verdanatesman/STM32-ile-BLDC-Motor-Surucu-Karti-Tasarimi-ve-Uretimi/Tasarım görseller/ek3.jpeg

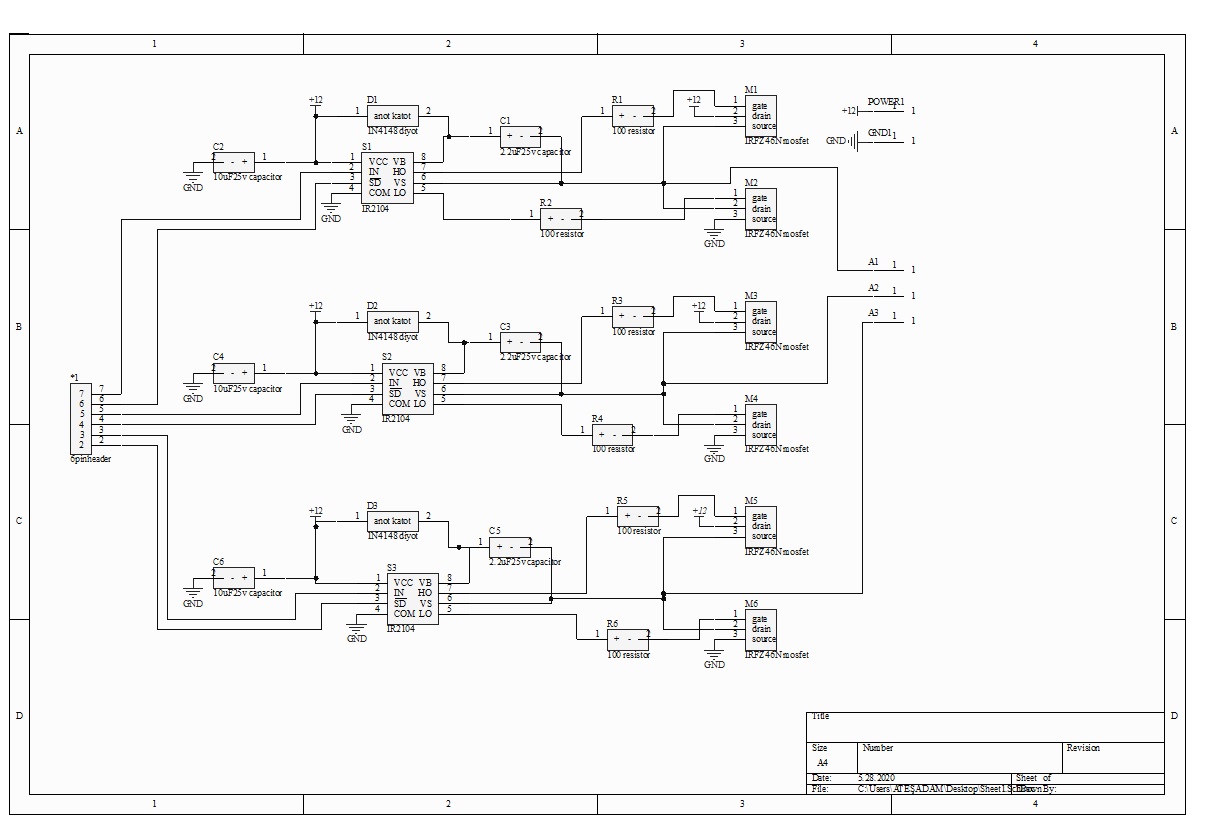
Tasarım görseller/ek3.jpeg
