verdanatesman/STM32-ile-BLDC-Motor-Surucu-Karti-Tasarimi-ve-Uretimi/Tasarım görseller/ek4.jpeg

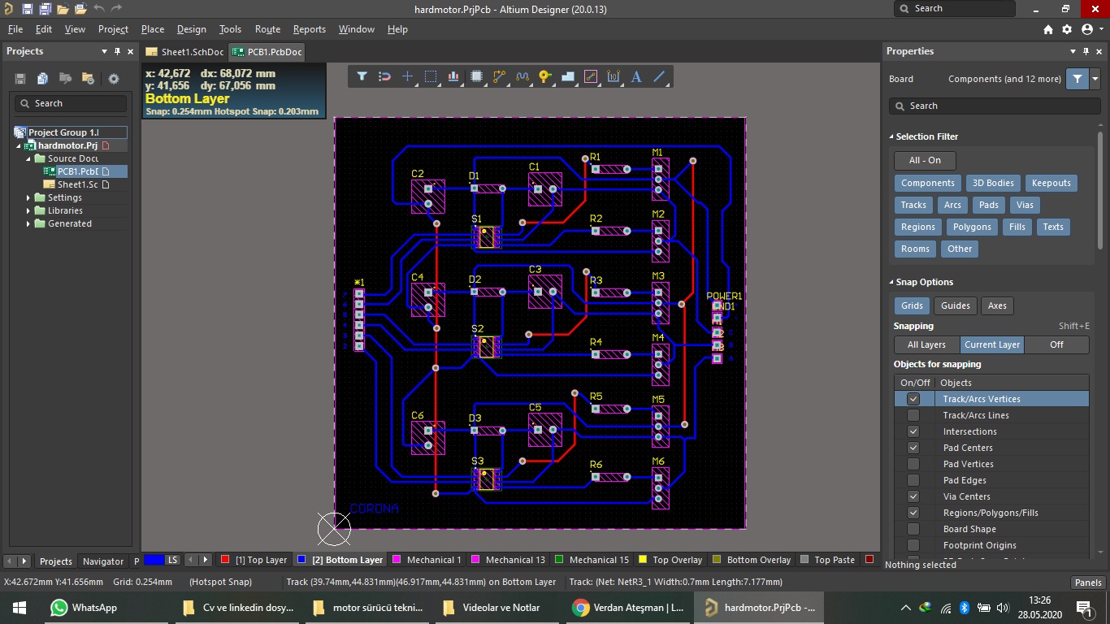
Tasarım görseller/ek4.jpeg
