verdanatesman/STM32-ile-BLDC-Motor-Surucu-Karti-Tasarimi-ve-Uretimi/Uretim gorselleri/ek7.jpeg

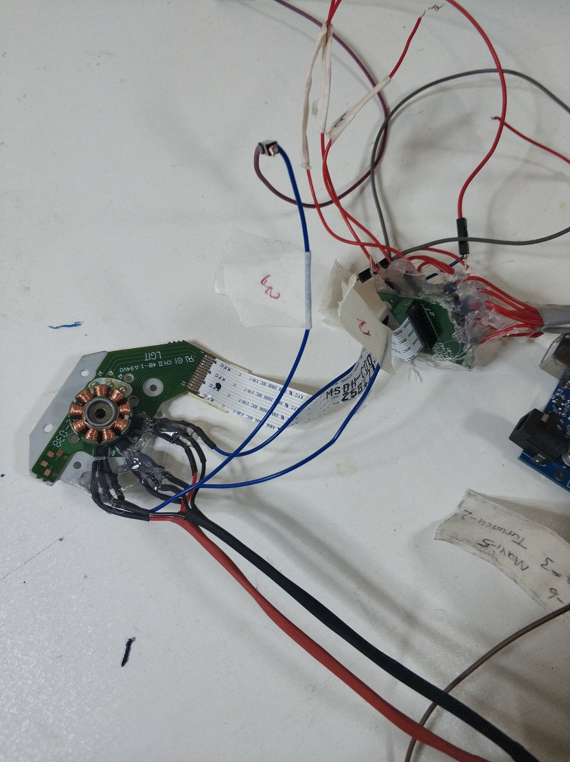
Uretim gorselleri/ek7.jpeg
