verdanatesman/STM32-ile-BLDC-Motor-Surucu-Karti-Tasarimi-ve-Uretimi/Uretim gorselleri/ek8.jpeg

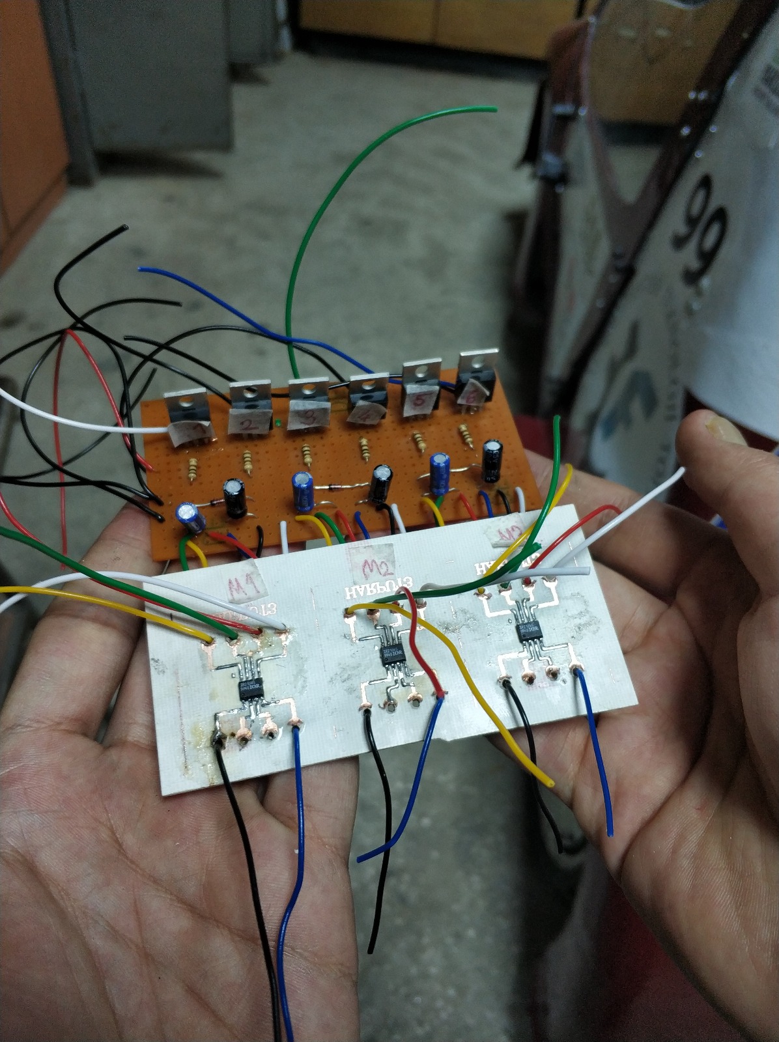
Uretim gorselleri/ek8.jpeg
