verdanatesman/STM32-ile-BLDC-Motor-Surucu-Karti-Tasarimi-ve-Uretimi/Uretim gorselleri/ek11.jpeg

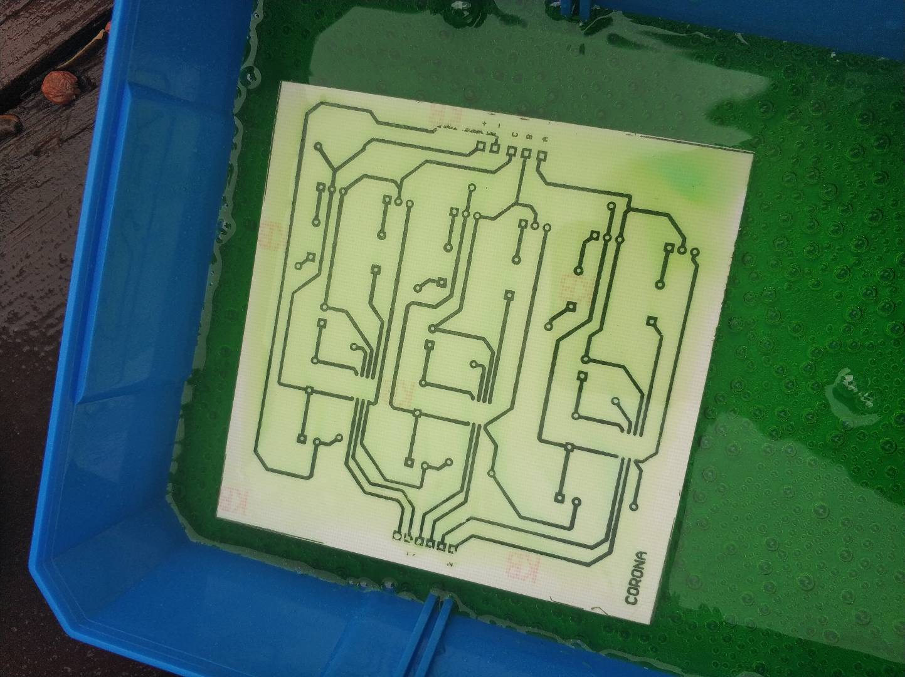
Uretim gorselleri/ek11.jpeg
