verdanatesman/STM32-ile-BLDC-Motor-Surucu-Karti-Tasarimi-ve-Uretimi/Uretim gorselleri/ek12.jpeg

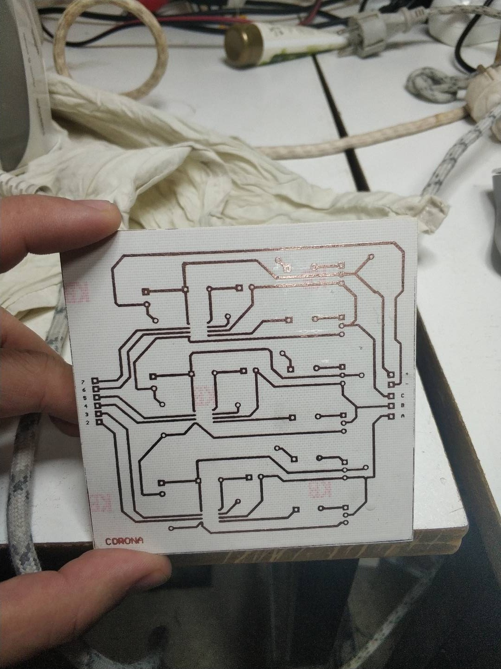
Uretim gorselleri/ek12.jpeg
