verdanatesman/STM32-ile-BLDC-Motor-Surucu-Karti-Tasarimi-ve-Uretimi/Uretim gorselleri/ek13.jpeg

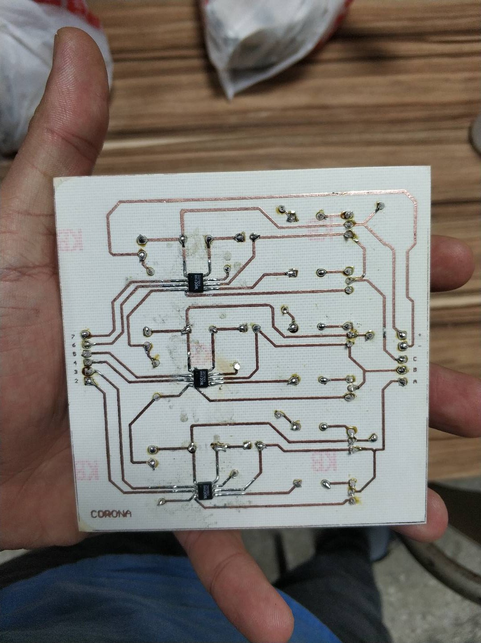
Uretim gorselleri/ek13.jpeg
