verdanatesman/STM32-ile-BLDC-Motor-Surucu-Karti-Tasarimi-ve-Uretimi/Uretim gorselleri/ek14.jpeg

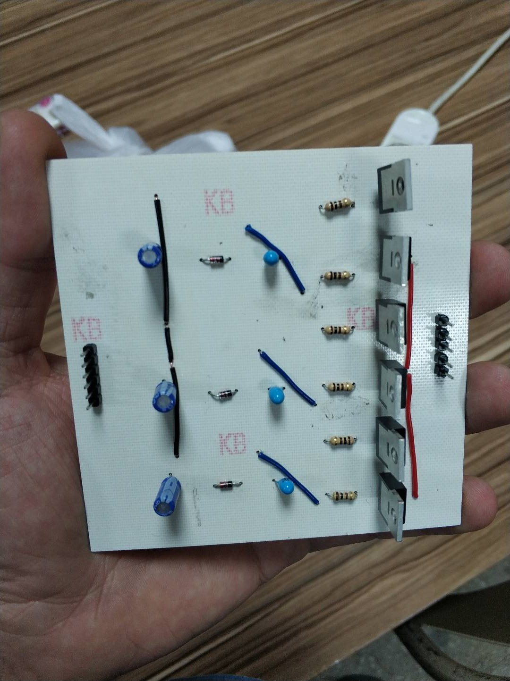
Uretim gorselleri/ek14.jpeg
