verdanatesman/STM32-ile-BLDC-Motor-Surucu-Karti-Tasarimi-ve-Uretimi/Uretim gorselleri/ek15.jpeg

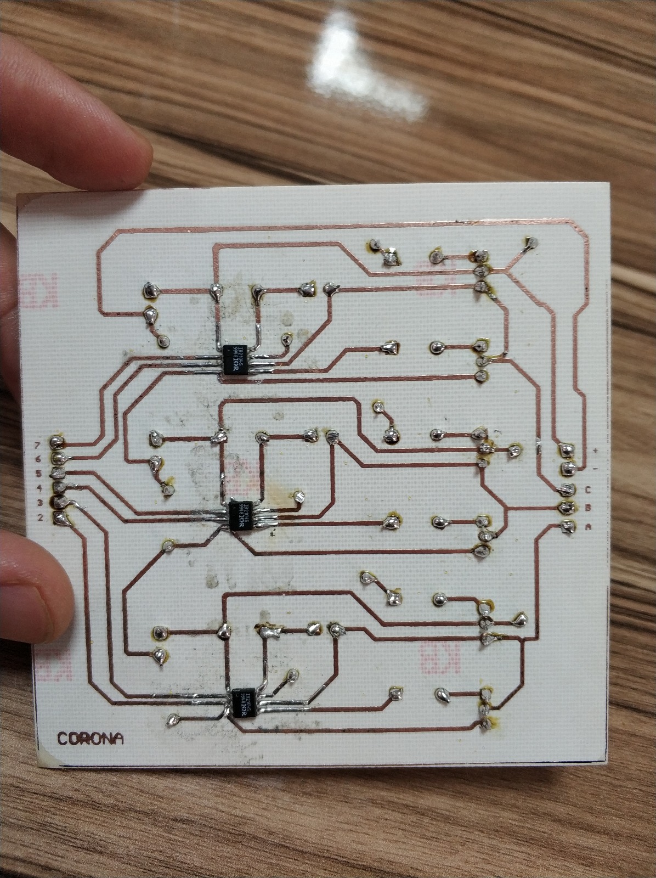
Uretim gorselleri/ek15.jpeg
