verdanatesman/STM32-ile-BLDC-Motor-Surucu-Karti-Tasarimi-ve-Uretimi/AltiumDesigner/IPM/Project Outputs for IPM/17-53.PDF

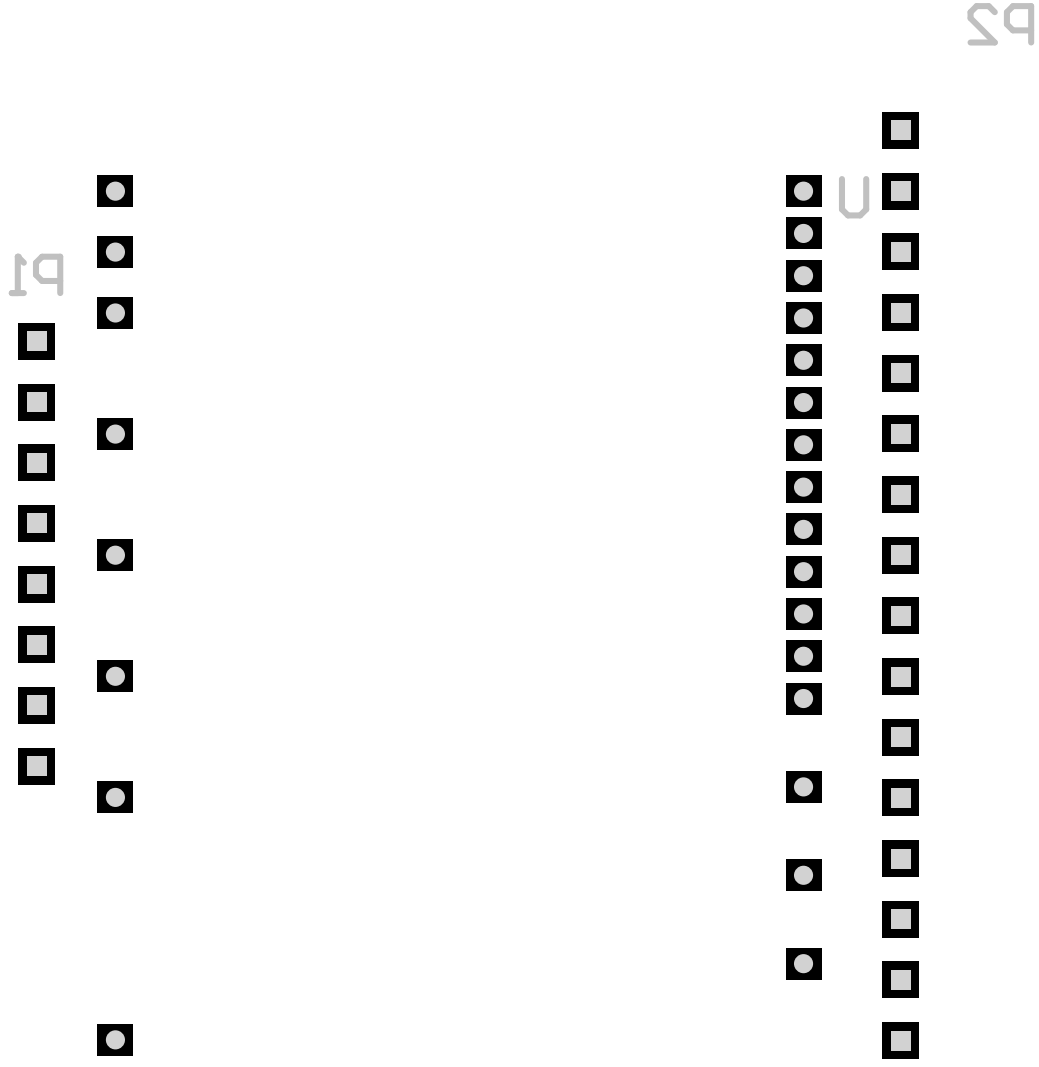
[picture p28: page 1]
