verdanatesman/STM32-ile-BLDC-Motor-Surucu-Karti-Tasarimi-ve-Uretimi/AltiumDesigner/IPM/Project Outputs for IPM/17-55.PDF

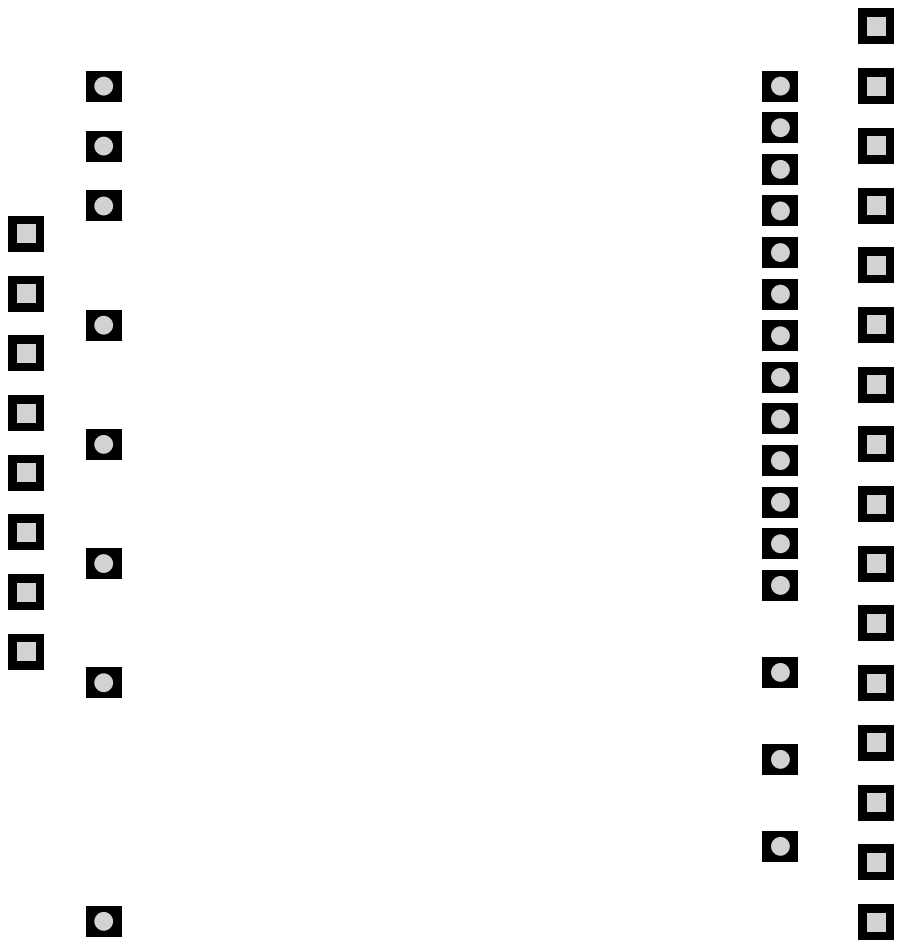
[picture p29: page 1]
