verdanatesman/STM32-ile-BLDC-Motor-Surucu-Karti-Tasarimi-ve-Uretimi/AltiumDesigner/IPM/Project Outputs for IPM/17-56.PDF

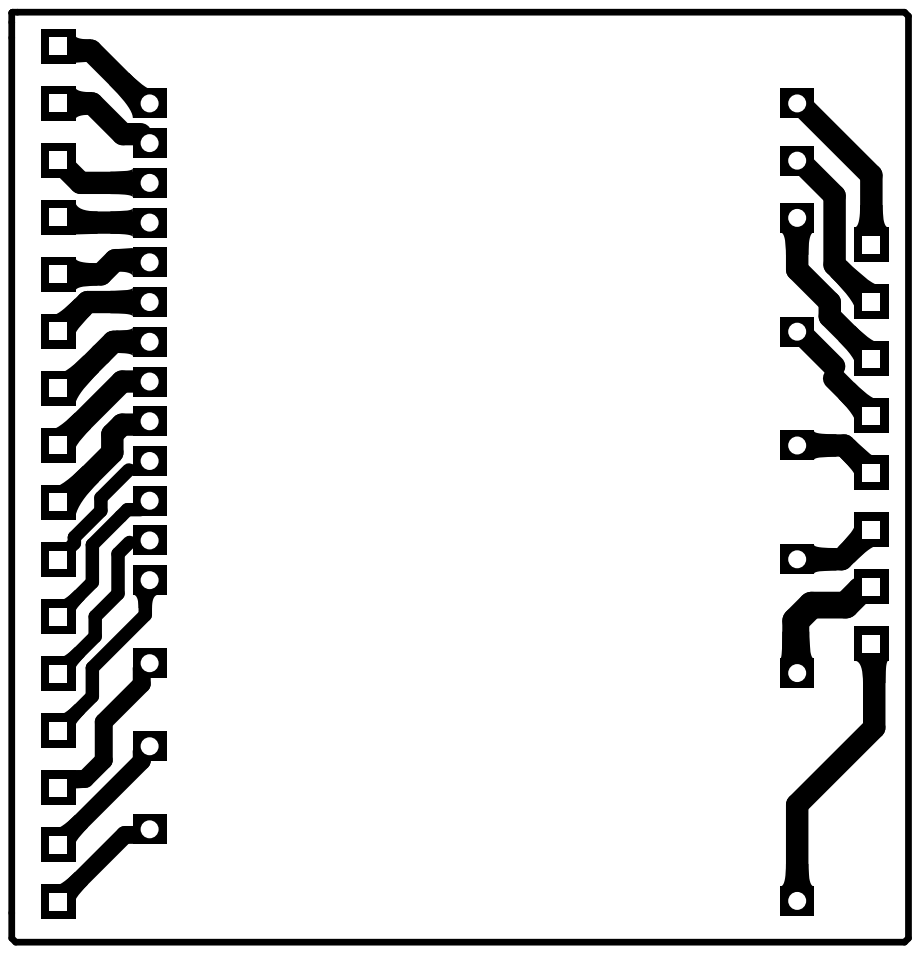
[picture p30: page 1]
