verdanatesman/STM32-ile-BLDC-Motor-Surucu-Karti-Tasarimi-ve-Uretimi/AltiumDesigner/IPM/Project Outputs for IPM/[No Variations].PDF

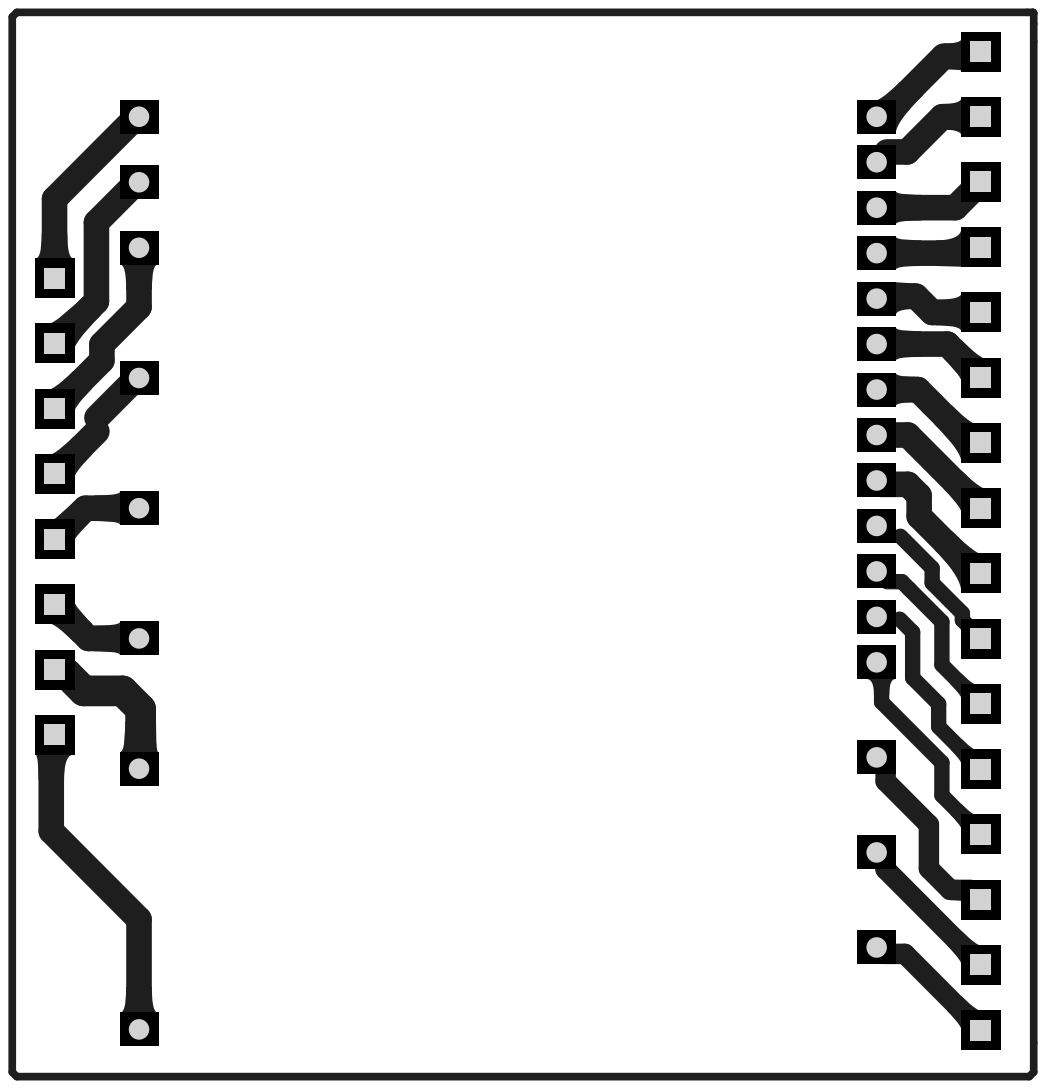
[picture p31: page 1]
