verdanatesman/STM32-ile-BLDC-Motor-Surucu-Karti-Tasarimi-ve-Uretimi/AltiumDesigner/hardmotor/Project Outputs for hardmotor/PDF/12-31.PDF

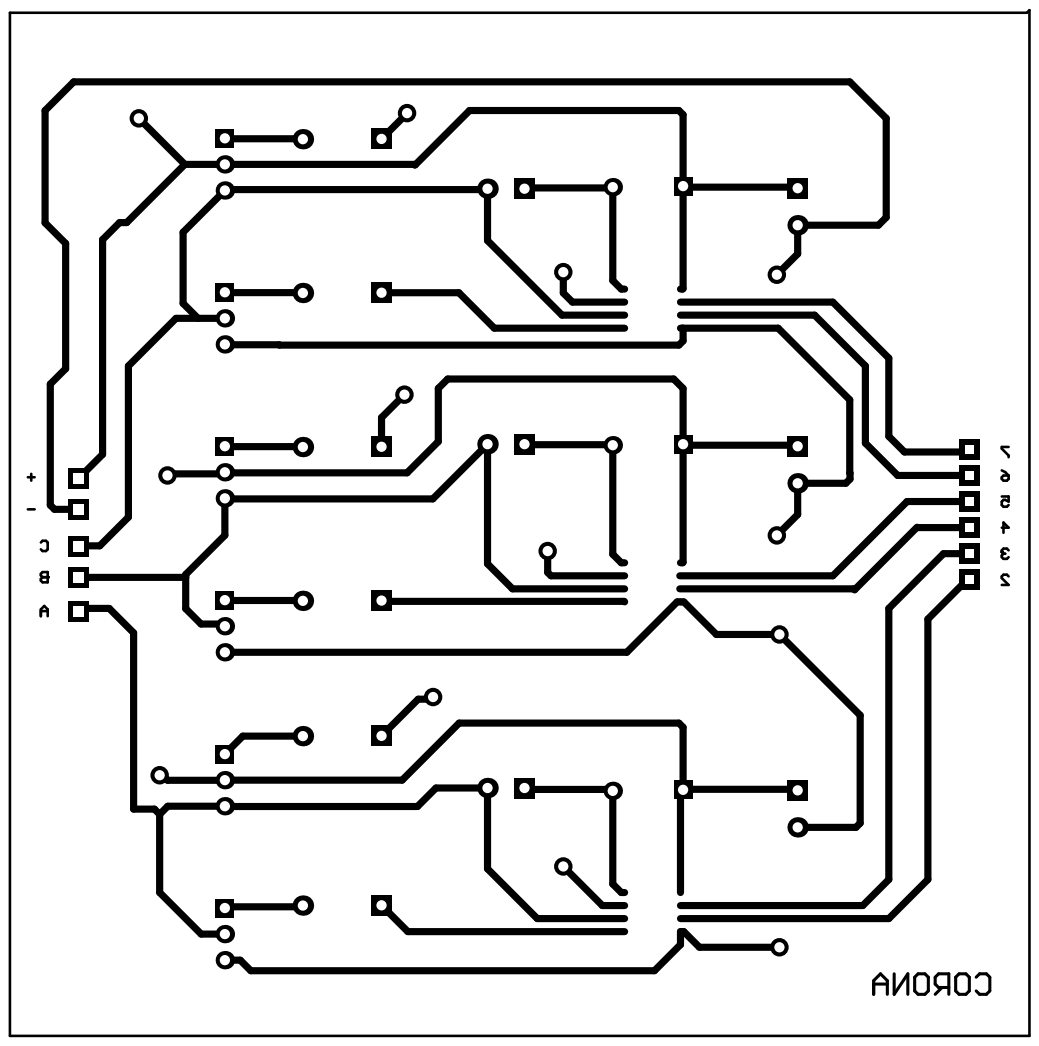
[picture p32: page 1]
