verdanatesman/STM32-ile-BLDC-Motor-Surucu-Karti-Tasarimi-ve-Uretimi/AltiumDesigner/hardmotor/Project Outputs for hardmotor/PDF/12-47.PDF

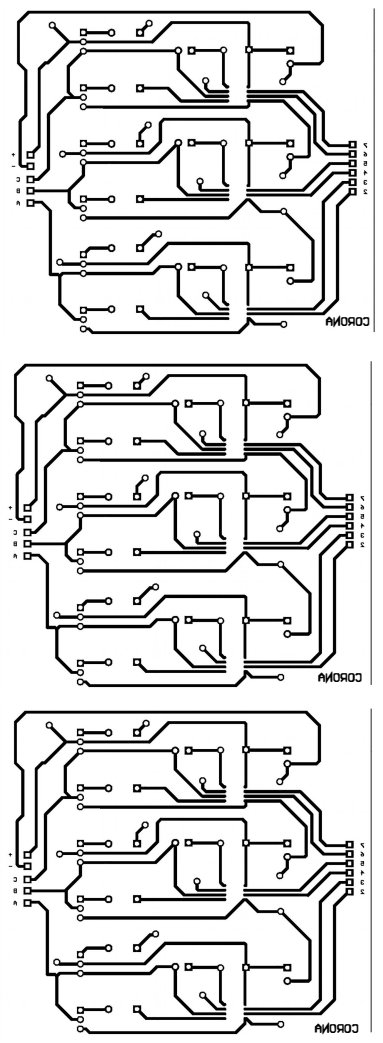
[picture p33: page 1]
