verdanatesman/STM32-ile-BLDC-Motor-Surucu-Karti-Tasarimi-ve-Uretimi/AltiumDesigner/hardmotor/Project Outputs for hardmotor/PDF/13-02.PDF

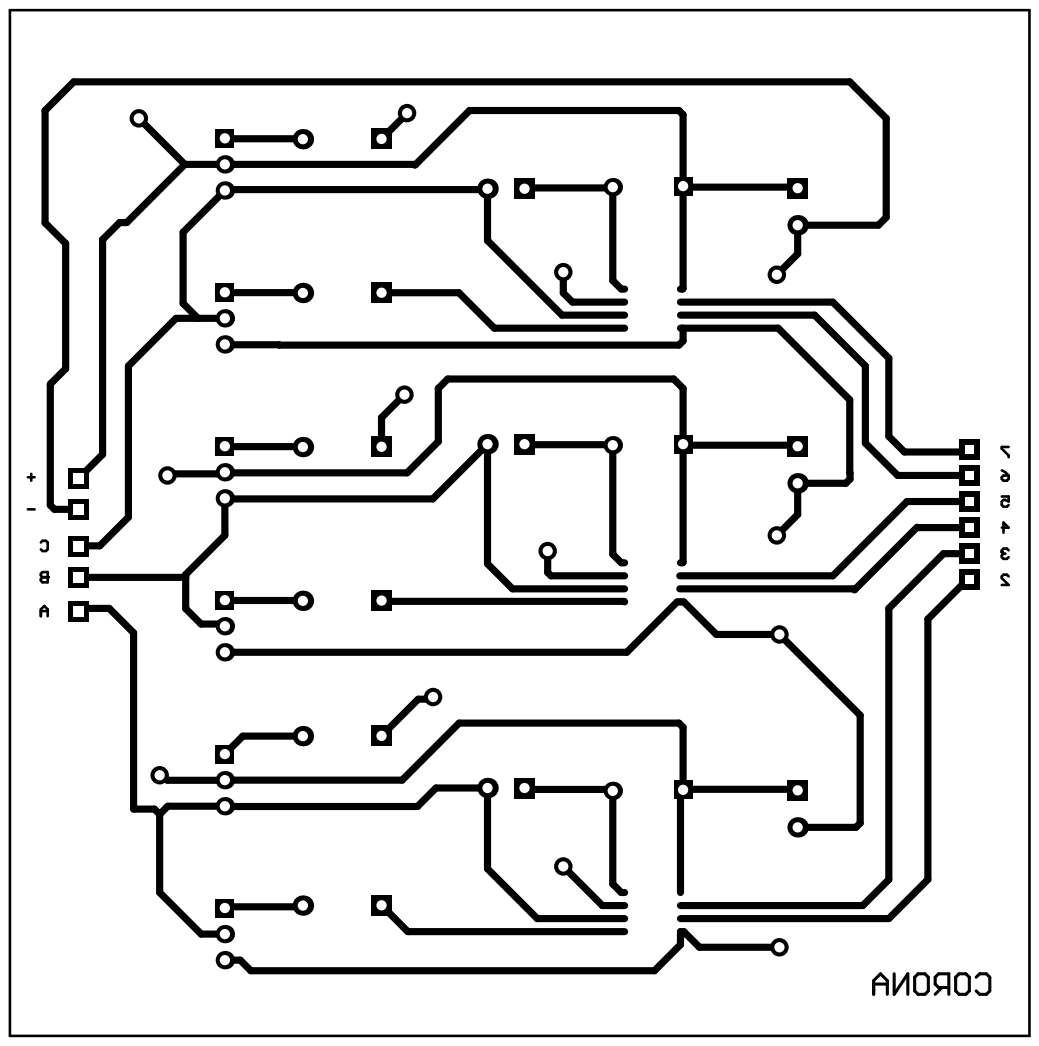
[picture p34: page 1]
