verdanatesman/STM32-ile-BLDC-Motor-Surucu-Karti-Tasarimi-ve-Uretimi/AltiumDesigner/IPM/Project Outputs for IPM/IPM/IPM.PDF

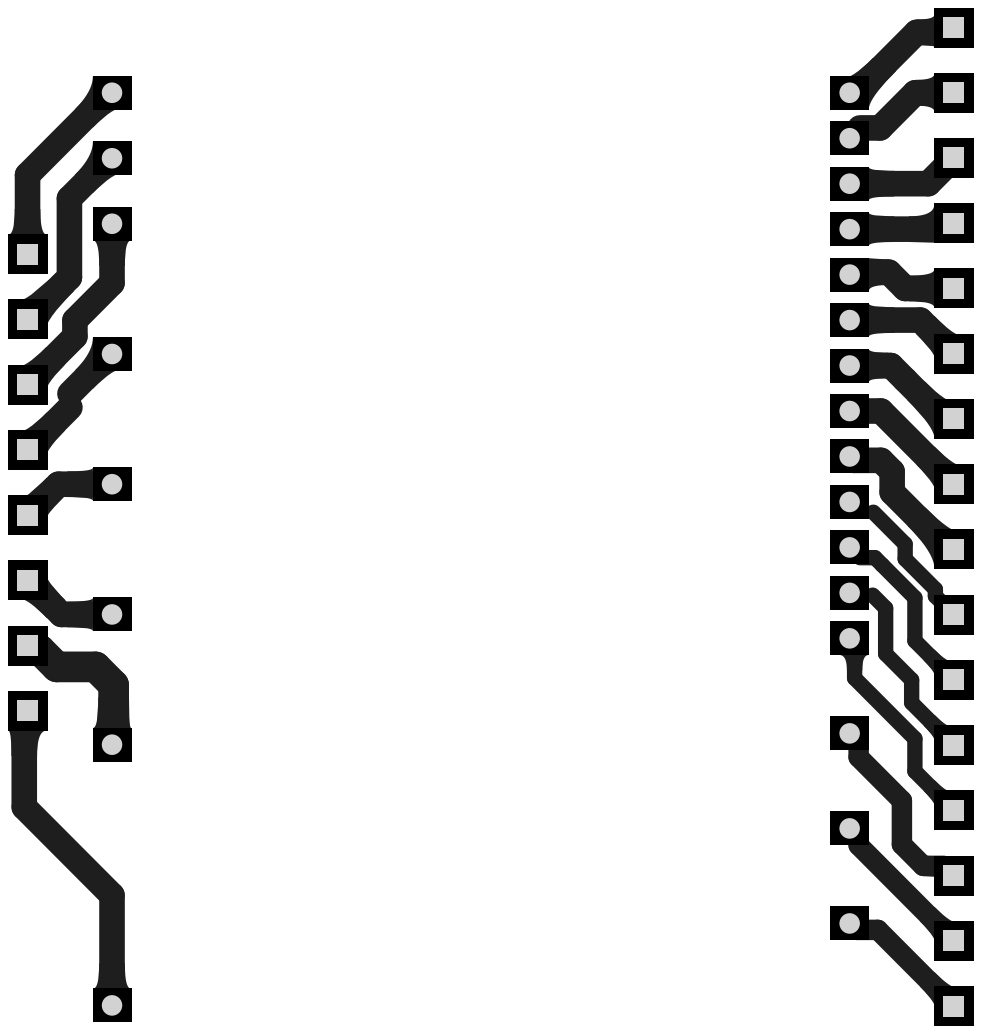
[picture p35: page 1]
